hancheyn/MicroDev-1.0.0/MDT0000_STLs_V20_/MDTM1103.STL

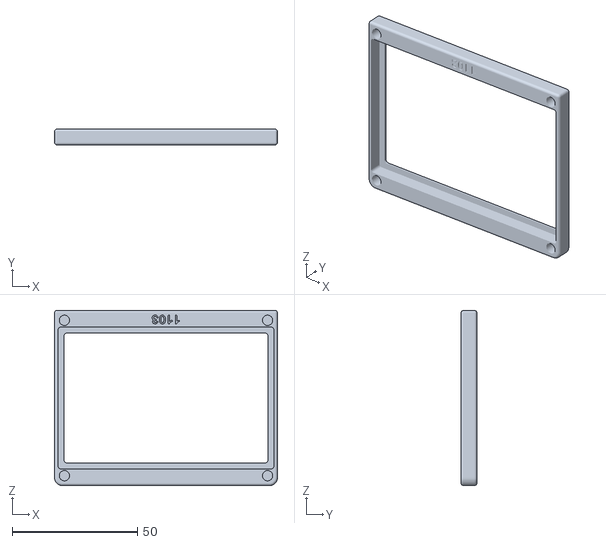
[picture p24: CAD file, 2022-11-06]
MDT0000_STLs_V20_/MDTM1103.STL
88.9 x 6.35 x 69.8
