hancheyn/MicroDev-1.0.0/MDT0000_STLs_V20_/MDTM1201.STL

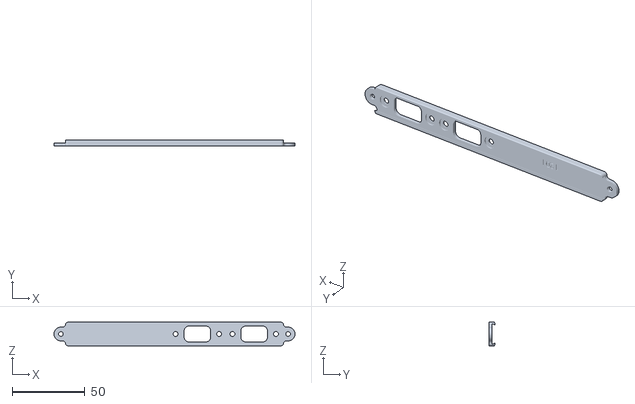
[picture p25: CAD file, 2022-11-06]
MDT0000_STLs_V20_/MDTM1201.STL
166.2 x 3.81 x 16.3
