hancheyn/MicroDev-1.0.0/MDT0000_STLs_V20_/MDTM4001.STL

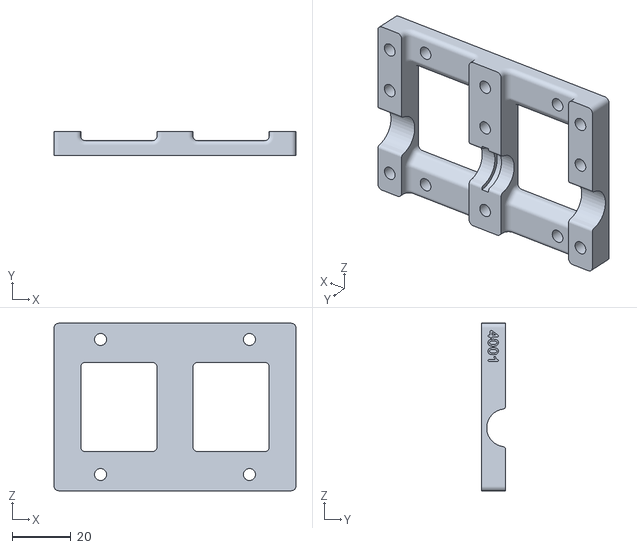
[picture p26: CAD file, 2022-11-06]
MDT0000_STLs_V20_/MDTM4001.STL
82.5 x 8.26 x 57.1
