hancheyn/MicroDev-1.0.0/MDT0000_STLs_V20_/MDTM4002.STL

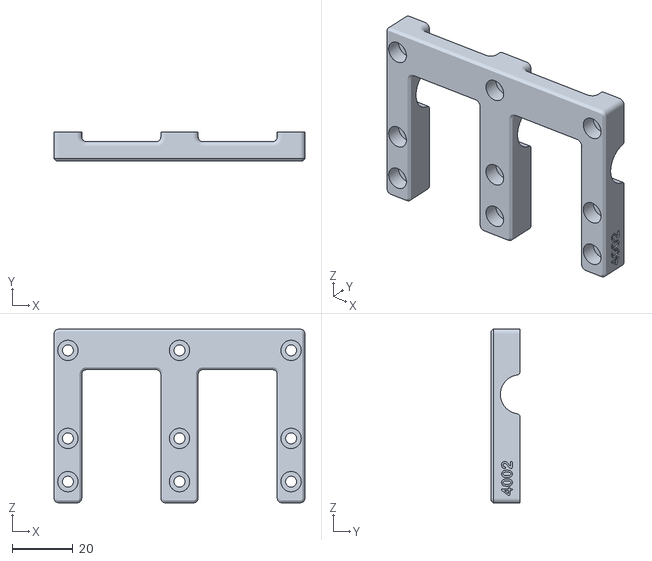
[picture p27: CAD file, 2022-11-06]
MDT0000_STLs_V20_/MDTM4002.STL
82.6 x 9.52 x 57.1
