hancheyn/MicroDev-1.0.0/MDT0000_STLs_V20_/MDTM2004_ARD.STL

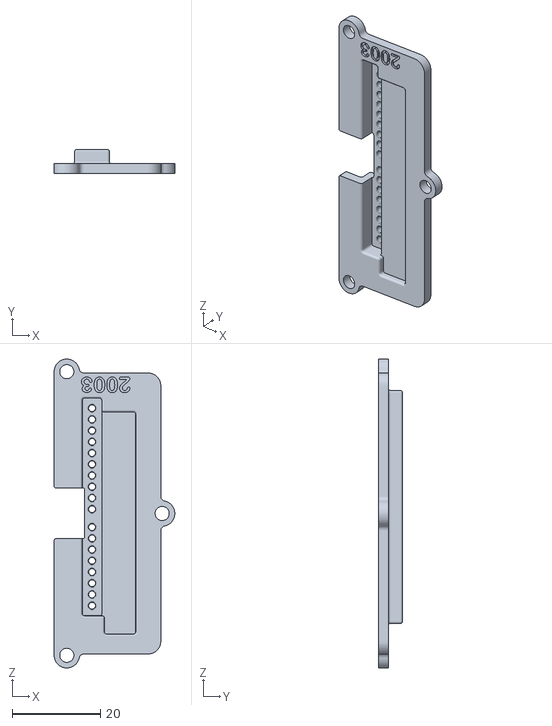
[picture p28: CAD file, 2022-11-06]
MDT0000_STLs_V20_/MDTM2004_ARD.STL
27.3 x 5.49 x 69.9
