hancheyn/MicroDev-1.0.0/MDT0000_STLs_V20_/MDTM1008.STL

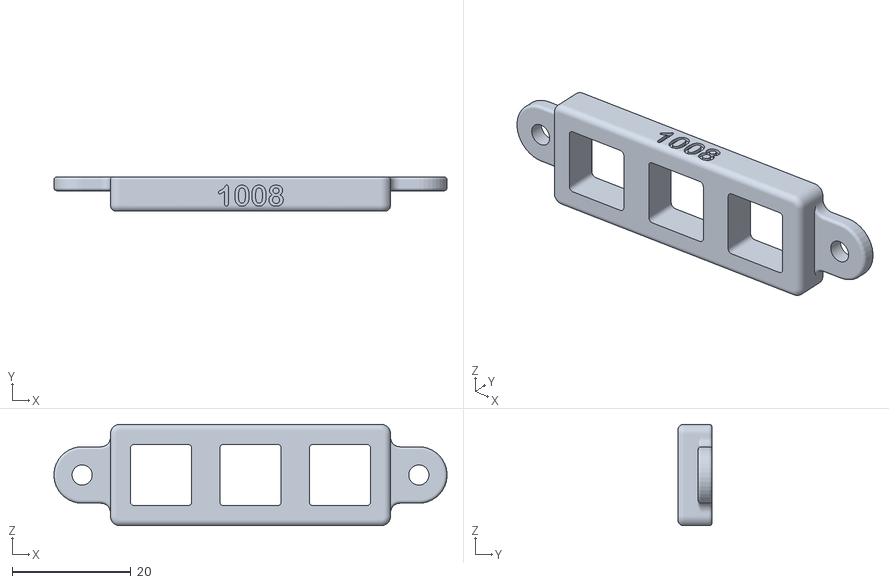
[picture p29: CAD file, 2022-11-06]
MDT0000_STLs_V20_/MDTM1008.STL
66.3 x 5.79 x 17.1
