hancheyn/MicroDev-1.0.0/MDT0000_STLs_V20_/MDTM2004_STM.STL

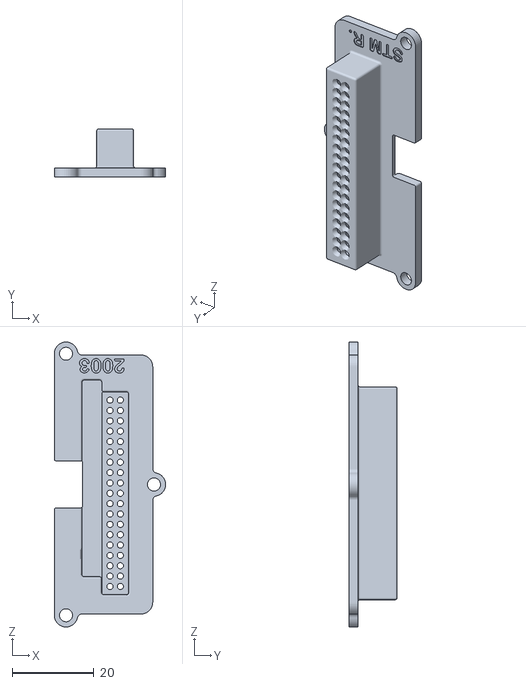
[picture p30: CAD file, 2022-11-06]
MDT0000_STLs_V20_/MDTM2004_STM.STL
27.3 x 11.9 x 69.9
