hancheyn/MicroDev-1.0.0/MDT0000_STLs_V20_/MDTM4009.STL

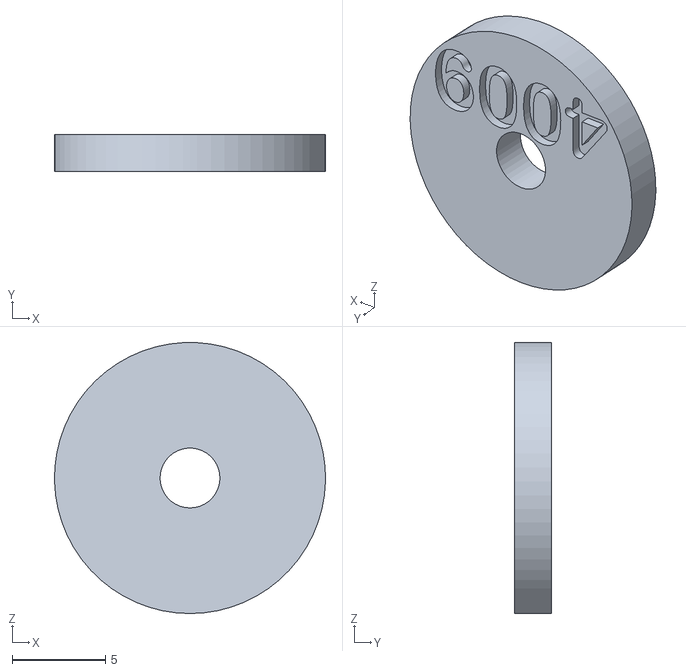
[picture p31: CAD file, 2022-11-06]
MDT0000_STLs_V20_/MDTM4009.STL
14.5 x 2.00 x 14.5
