hancheyn/MicroDev-1.0.0/MDT0000_STLs_V20_/MDTM4008.STL

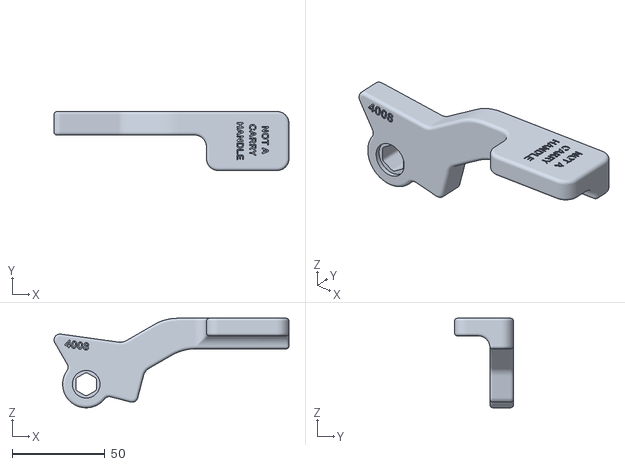
[picture p32: CAD file, 2022-11-06]
MDT0000_STLs_V20_/MDTM4008.STL
126.5 x 31.8 x 48.2
