hancheyn/MicroDev-1.0.0/MDT0000_STLs_V20_/MDTM2002.STL

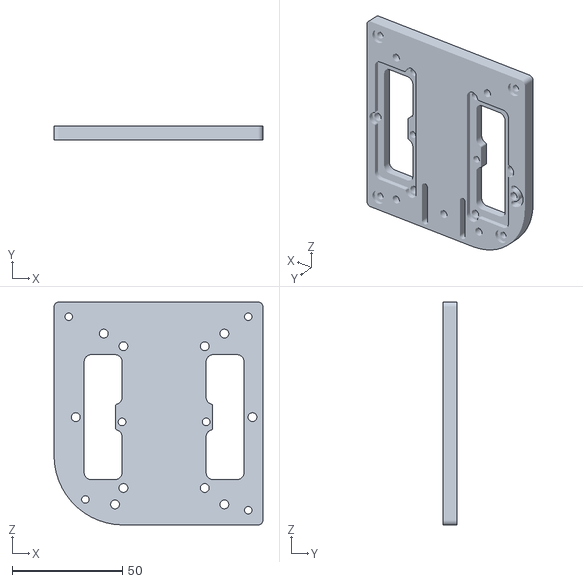
[picture p33: CAD file, 2022-11-06]
MDT0000_STLs_V20_/MDTM2002.STL
94.7 x 6.35 x 101.0
