hancheyn/MicroDev-1.0.0/MDT0000_STLs_V20_/MDTM1101.STL

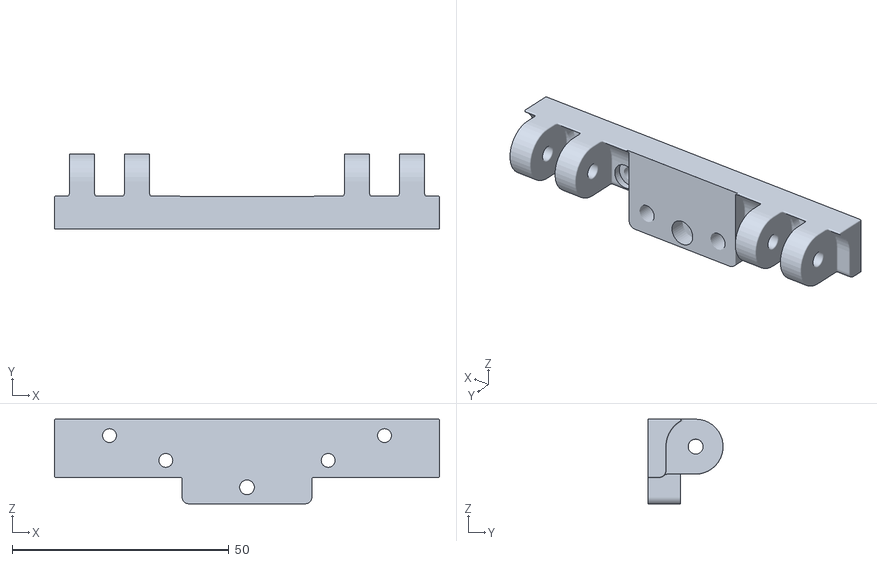
[picture p34: CAD file, 2022-11-06]
MDT0000_STLs_V20_/MDTM1101.STL
88.9 x 17.4 x 19.6
