hancheyn/MicroDev-1.0.0/MDT0000_STLs_V20_/MDTM1104.STL

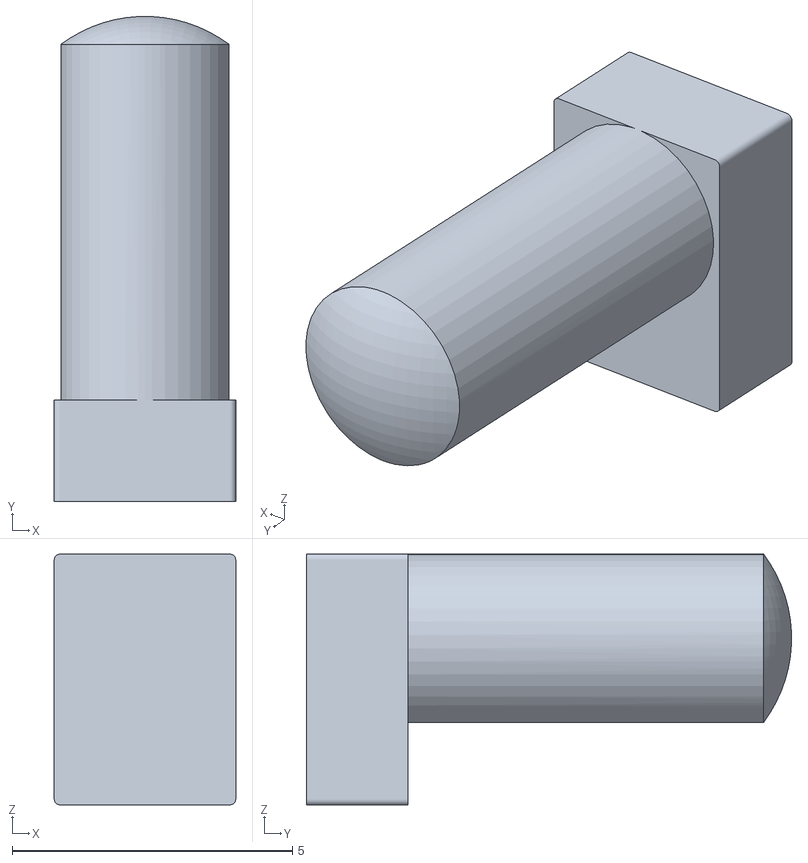
[picture p35: CAD file, 2022-11-06]
MDT0000_STLs_V20_/MDTM1104.STL
3.24 x 8.65 x 4.47
