hancheyn/MicroDev-1.0.0/MDT0000_STLs_V20_/MDTM1004.STL

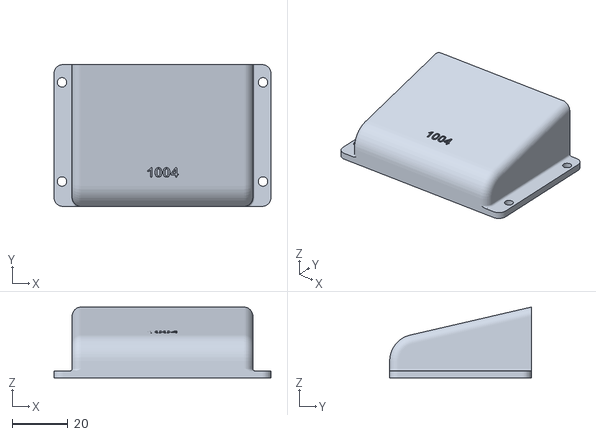
[picture p36: CAD file, 2022-11-06]
MDT0000_STLs_V20_/MDTM1004.STL
77.8 x 50.8 x 25.4
