hancheyn/MicroDev-1.0.0/MDT0000_STLs_V20_/MDTM3001.STL

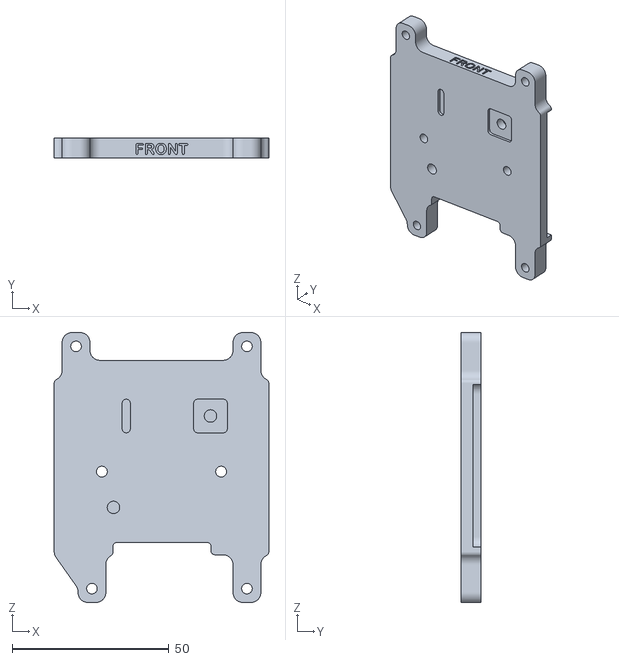
[picture p37: CAD file, 2022-11-06]
MDT0000_STLs_V20_/MDTM3001.STL
68.6 x 6.35 x 86.3
