hancheyn/MicroDev-1.0.0/MDT0000_STLs_V20_/MDTM0003.STL

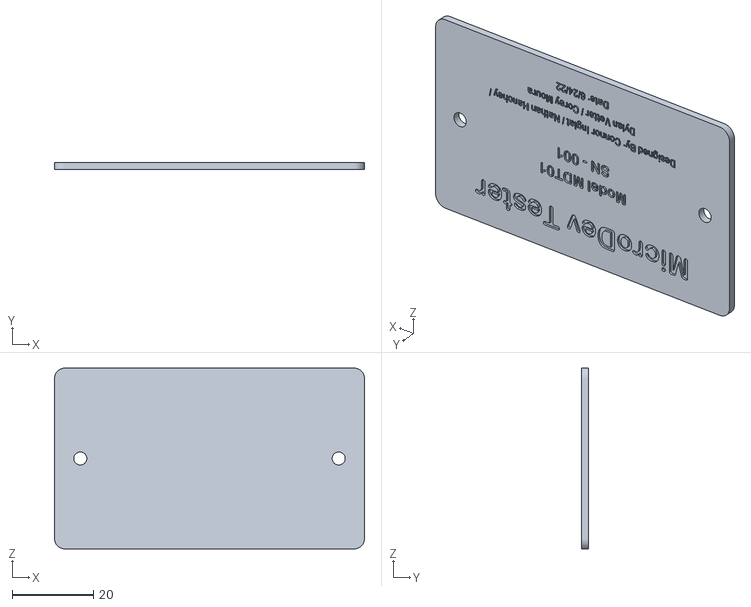
[picture p38: CAD file, 2022-11-06]
MDT0000_STLs_V20_/MDTM0003.STL
76.2 x 1.63 x 44.5
