hancheyn/MicroDev-1.0.0/MDT0000_STLs_V20_/MDTM4004.STL

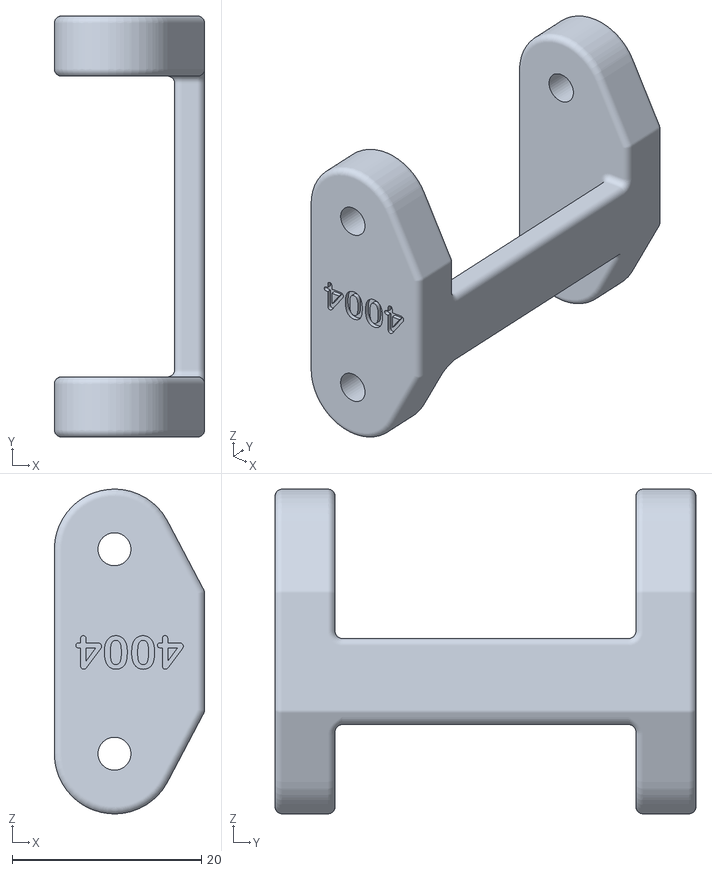
[picture p39: CAD file, 2022-11-06]
MDT0000_STLs_V20_/MDTM4004.STL
15.9 x 44.5 x 34.3
